jpetrocik/sprintmeter-firmware/android/app/src/main/java/com/bmxgates/logger/BluetoothSerial.java

package com.bmxgates.logger;

import android.app.AlertDialog;
import android.app.Dialog;
import android.bluetooth.BluetoothAdapter;
import android.bluetooth.BluetoothDevice;
import android.bluetooth.BluetoothSocket;
import android.content.BroadcastReceiver;
import android.content.Context;
import android.content.Intent;
import android.content.IntentFilter;
import android.os.AsyncTask;
import android.support.v4.content.LocalBroadcastManager;
import android.util.Log;

import java.io.IOException;
import java.io.InputStream;
import java.io.OutputStream;
import java.lang.reflect.Method;
import java.util.ArrayList;
import java.util.List;
import java.util.UUID;

/**
 * Provides a high level wrapper around all the lower level bluetooth operations. Handles connecting to,
 * reestablishing connections, and reading from the serialInputStream.
 *   
 * @author jpetrocik
 *
 */
public class BluetoothSerial {

	public static final String BLUETOOTH_CONNECTED = "bluetooth-connection-started";
	
	public static final String BLUETOOTH_DISCONNECTED = "bluetooth-connection-lost";

	public static final String BLUETOOTH_FAILED = "bluetooth-connection-failed";

	public static final int MAX_ATTEMPTS = 3;
	

	boolean connected = false;
	
	BluetoothDevice bluetoothDevice;
	
	BluetoothSocket serialSocket;

	InputStream serialInputStream;

	OutputStream serialOutputStream;

	SerialReader serialReader;
	
	MessageHandler messageHandler;
	
	Context context;
	
	AsyncTask<Void, Void, BluetoothDevice> connectionTask;
	
	String devicePrefix;
	
	/**
	 * Listens for discount message from bluetooth system and try reestablishing a connection
	 */
	private final BroadcastReceiver bluetoothReceiver = new BroadcastReceiver() {
		@Override
		public void onReceive(Context context, Intent intent) {
			String action = intent.getAction();
			BluetoothDevice eventDevice = intent.getParcelableExtra(BluetoothDevice.EXTRA_DEVICE);

			if (BluetoothDevice.ACTION_ACL_DISCONNECTED.equals(action)) {
				if (bluetoothDevice != null && bluetoothDevice.equals(eventDevice)){
					Log.i(BluetoothSerial.class.getName(), "Received bluetooth disconnect notice. Status: " + (connected?"Connected":"Disconnected"));
					
					if (connected){
						//clean up any streams
						close();
						
						//reestablish connect
						connect();
						
						LocalBroadcastManager.getInstance(context).sendBroadcast(new Intent(BLUETOOTH_DISCONNECTED));
					}
				}
			}           
		}
	};
	
	public BluetoothSerial(Context context, MessageHandler messageHandler, String devicePrefix){
		this.context = context;
		this.messageHandler = messageHandler;
		this.devicePrefix = devicePrefix;
	}

	public void onPause() {
		context.unregisterReceiver(bluetoothReceiver);
	}

	public void onResume() {
		//listen for bluetooth disconnect
		IntentFilter disconnectIntent = new IntentFilter(BluetoothDevice.ACTION_ACL_DISCONNECTED);
		context.registerReceiver(bluetoothReceiver, disconnectIntent);
		
		//reestablishes a connection is one doesn't exist
		if(!connected){
			connect();
			Intent intent = new Intent(BLUETOOTH_DISCONNECTED);
			LocalBroadcastManager.getInstance(context).sendBroadcast(intent);
		} else {
			Intent intent = new Intent(BLUETOOTH_CONNECTED);
			LocalBroadcastManager.getInstance(context).sendBroadcast(intent);
		}
	}


	/**
	 * Initializes the bluetooth serial connections, uses the LocalBroadcastManager when
	 * connection is established
	 */
	public void connect(){

		if (connected){
			Log.i(BluetoothSerial.class.getName(),"Connection request while already connected");
			return;
		}

		if (connectionTask != null && connectionTask.getStatus()==AsyncTask.Status.RUNNING){
			Log.i(BluetoothSerial.class.getName(),"Connection request while attempting connection");
			return;
		}

		BluetoothAdapter bluetoothAdapter = BluetoothAdapter.getDefaultAdapter();
		if (bluetoothAdapter== null || !bluetoothAdapter.isEnabled()) {
			return;
		}

		final List<BluetoothDevice> pairedDevices = new ArrayList<BluetoothDevice>(bluetoothAdapter.getBondedDevices());
		if (pairedDevices.size() > 0) {
			bluetoothAdapter.cancelDiscovery();
			
			/**
			 * AsyncTask to handle the establishing of a bluetooth connection
			 */
			connectionTask = new AsyncTask<Void, Void, BluetoothDevice>(){

				int attemptCounter = 0;
				
				@Override
				protected BluetoothDevice doInBackground(Void... params) {
					while(!isCancelled()){ //need to kill without calling onCancel

						for (BluetoothDevice device : pairedDevices) {
							if (device.getName().startsWith(devicePrefix)){
								Log.i(BluetoothSerial.class.getName(), attemptCounter + ": Attempting connection to " + device.getName());

								try {
									
									try {
										// Standard SerialPortService ID
										UUID uuid = UUID.fromString("00001101-0000-1000-8000-00805F9B34FB"); 
										serialSocket = device.createRfcommSocketToServiceRecord(uuid);
									} catch (Exception ce){
										serialSocket = connectViaReflection(device);
									}
									
									//setup the connect streams
									serialSocket.connect();
									serialInputStream = serialSocket.getInputStream();
									serialOutputStream = serialSocket.getOutputStream();

									connected = true;
									Log.i(BluetoothSerial.class.getName(),"Connected to " + device.getName());

									return device;
								} catch (Exception e) {
									serialSocket = null;
									serialInputStream=null;
									serialOutputStream=null;
									Log.i(BluetoothSerial.class.getName(), "Failed to connect to " + device.getName(), e);
								}
							}
						}

						try {
							attemptCounter++;
							if (attemptCounter>MAX_ATTEMPTS)
								this.cancel(false);
							else
								Thread.sleep(1000);
						} catch (InterruptedException e) {
							break;
						}
					}

					Log.i(BluetoothSerial.class.getName(), "Stopping connection attempts");
					
					Intent intent = new Intent(BLUETOOTH_FAILED);
					LocalBroadcastManager.getInstance(context).sendBroadcast(intent);

					return null;
				}

				@Override
				protected void onPostExecute(BluetoothDevice result) {
					super.onPostExecute(result);

					bluetoothDevice = result;
					
					//start thread responsible for reading from inputstream
					serialReader = new SerialReader();
					serialReader.start();
					
					//send connection message
					Intent intent = new Intent(BLUETOOTH_CONNECTED);
					LocalBroadcastManager.getInstance(context).sendBroadcast(intent);
				}

			};
			connectionTask.execute();
		}
	}

	// see: http://stackoverflow.com/questions/3397071/service-discovery-failed-exception-using-bluetooth-on-android
	private BluetoothSocket connectViaReflection(BluetoothDevice device) throws Exception {
		Method m = device.getClass().getMethod("createRfcommSocket", new Class[] {int.class});
		return (BluetoothSocket) m.invoke(device, 1);
	}

	public int available() throws IOException{
		if (connected)
			return serialInputStream.available();
		
		throw new RuntimeException("Connection lost, reconnecting now.");
	}
	
	public int read() throws IOException{
		if (connected)
			return serialInputStream.read();
		
		throw new RuntimeException("Connection lost, reconnecting now.");
	}
	
	public int read(byte[] buffer) throws IOException{
		if (connected)
			return serialInputStream.read(buffer);
		
		throw new RuntimeException("Connection lost, reconnecting now.");
	}
	
	public int read(byte[] buffer, int byteOffset, int byteCount) throws IOException{
		if (connected)
			return serialInputStream.read(buffer, byteOffset, byteCount);
		
		throw new RuntimeException("Connection lost, reconnecting now.");
	}

	public void write(byte[] buffer) throws IOException{
		if (!connected)
			throw new RuntimeException("Connection lost, reconnecting now.");

		serialOutputStream.write(buffer);
	}
	
	public void write(int oneByte) throws IOException{
		if (!connected)
			throw new RuntimeException("Connection lost, reconnecting now.");

		serialOutputStream.write(oneByte);
	}
	
	public void write(byte[] buffer, int offset, int count) throws IOException {
		if (!connected)
			throw new RuntimeException("Connection lost, reconnecting now.");

		serialOutputStream.write(buffer, offset, count);
		
	}
	
	private class SerialReader extends Thread {
		private static final int MAX_BYTES = 125;
		
		byte[] buffer = new byte[MAX_BYTES];

		int bufferSize = 0;

		public void run() {
			Log.i(BluetoothSerial.class.getName(), "Starting serial loop");
			while (!isInterrupted()) {
				try {

					/*
					 * check for some bytes, or bytes still left in
					 * buffer
					 */
					if (available() > 0){ 
						
						int newBytes = read(buffer, bufferSize, MAX_BYTES - bufferSize);
						if (newBytes > 0)
							bufferSize += newBytes;

//						Log.v(BMX_BLUETOOTH, "read " + newBytes);
					}
					
					if (bufferSize > 0) {	
						int read = messageHandler.read(bufferSize, buffer);

						// shift unread data to start of buffer
						if (read > 0) {
							int index = 0;
							for (int i = read; i < bufferSize; i++) {
								buffer[index++] = buffer[i];
							}
							bufferSize = index;
						}
					} else {
						
						try {
							if (bufferSize == 0)
								Thread.sleep(10);
						} catch (InterruptedException ie) {
							break;
						}
					}
				} catch (Exception e) {
					Log.e(BluetoothSerial.class.getName(), "Error reading serial data", e);
				}
			}
			Log.i(BluetoothSerial.class.getName(), "Shutting serial loop");
		}
	};
	
	/**
	 * Reads from the serial buffer, processing any available messages.  Must return the number of bytes 
	 * consumer from the buffer
	 * 
	 * @author jpetrocik
	 *
	 */
	public static interface MessageHandler {
		public int read(int bufferSize, byte[] buffer);
	}

	public void close() {
		
		connected = false;
		
		if (serialReader != null) {
			serialReader.interrupt();
		
			try {
				serialReader.join(1000);
			} catch (InterruptedException ie) {}
		}
		
		try {
			serialInputStream.close();
		} catch (Exception e) {
			Log.e(BluetoothSerial.class.getName(), "Failed releasing inputstream connection");
		}

		try {
			serialOutputStream.close();
		} catch (Exception e) {
			Log.e(BluetoothSerial.class.getName(), "Failed releasing outputstream connection");
		}

		try {
			serialSocket.close();
		} catch (Exception e) {
			Log.e(BluetoothSerial.class.getName(), "Failed closing socket");
		}

		Log.i(BluetoothSerial.class.getName(), "Released bluetooth connections");
		
	}

	static public Dialog connectionDialog(Context context){
		AlertDialog.Builder builder = new AlertDialog.Builder(context);
		builder.setIcon(R.drawable.bluetooth_logo)
		.setTitle("Connecting...");

		Dialog dialog = builder.create();
		dialog.show();
		
		return dialog;

	}

}
